akpeisov/MainControllerNew/main/temp.c

/* Simple handler for light brightness control */
static esp_err_t light_brightness_post_handler(httpd_req_t *req)
{
    int total_len = req->content_len;
    int cur_len = 0;
    char *buf = ((rest_server_context_t *)(req->user_ctx))->scratch;
    int received = 0;
    if (total_len >= SCRATCH_BUFSIZE) {
        /* Respond with 500 Internal Server Error */
        httpd_resp_send_err(req, HTTPD_500_INTERNAL_SERVER_ERROR, "content too long");
        return ESP_FAIL;
    }
    while (cur_len < total_len) {
        received = httpd_req_recv(req, buf + cur_len, total_len);
        if (received <= 0) {
            /* Respond with 500 Internal Server Error */
            httpd_resp_send_err(req, HTTPD_500_INTERNAL_SERVER_ERROR, "Failed to post control value");
            return ESP_FAIL;
        }
        cur_len += received;
    }
    buf[total_len] = '\0';

    cJSON *root = cJSON_Parse(buf);
    int red = cJSON_GetObjectItem(root, "red")->valueint;
    int green = cJSON_GetObjectItem(root, "green")->valueint;
    int blue = cJSON_GetObjectItem(root, "blue")->valueint;
    ESP_LOGI(TAG, "Light control: red = %d, green = %d, blue = %d", red, green, blue);
    cJSON_Delete(root);
    httpd_resp_sendstr(req, "Post control value successfully");
    return ESP_OK;
}

/* Simple handler for getting system handler */
static esp_err_t system_info_get_handler(httpd_req_t *req)
{
    httpd_resp_set_type(req, "application/json");
    cJSON *root = cJSON_CreateObject();
    esp_chip_info_t chip_info;
    esp_chip_info(&chip_info);
    cJSON_AddStringToObject(root, "version", IDF_VER);
    cJSON_AddNumberToObject(root, "cores", chip_info.cores);
    const char *sys_info = cJSON_Print(root);
    httpd_resp_sendstr(req, sys_info);
    free((void *)sys_info);
    cJSON_Delete(root);
    return ESP_OK;
}

/* Simple handler for getting temperature data */
static esp_err_t temperature_data_get_handler(httpd_req_t *req)
{
    httpd_resp_set_type(req, "application/json");
    cJSON *root = cJSON_CreateObject();
    cJSON_AddNumberToObject(root, "raw", esp_random() % 20);
    const char *sys_info = cJSON_Print(root);
    httpd_resp_sendstr(req, sys_info);
    free((void *)sys_info);
    cJSON_Delete(root);
    return ESP_OK;
}
